LonghornEngineer/DOOM_SAO/Software/DOOM_SAO/DG_Faces.h

/*****************************************************************************
 * Made with beer and late nights in California and Texas.
 *
 * (C) Copyright 2017-2019 AND!XOR LLC (https://andnxor.com/).
 *
 * PROPRIETARY AND CONFIDENTIAL UNTIL AUGUST 11th, 2019 then,
 *
 * Licensed under the Apache License, Version 2.0 (the "License");
 * you may not use this file except in compliance with the License.
 * You may obtain a copy of the License at
 *
 *     http://www.apache.org/licenses/LICENSE-2.0
 *
 * Unless required by applicable law or agreed to in writing, software
 * distributed under the License is distributed on an "AS IS" BASIS,
 * WITHOUT WARRANTIES OR CONDITIONS OF ANY KIND, either express or implied.
 * See the License for the specific language governing permissions and
 * limitations under the License.
 *
 * ADDITIONALLY:
 * If you find this source code useful in anyway, use it in another electronic
 * conference badge, or just think it's neat. Consider buying us a beer
 * (or two) and/or a badge (or two). We are just as obsessed with collecting
 * badges as we are in making them.
 *
 * Contributors:
 *  @Cr4bf04m
 *  @andnxor
 *  @zappbrandnxor
 *  @hyr0n1
 *  @bender_andnxor
 *  @lacosteaef
 *  @f4nci3
 ****************************************************************************
 */
 
/*
 * Contains all the Doomguy Faces
 * 
 * dg_FullHP_left
 * dg_FullHP_middle
 * dg_FullHP_right
 * dg_FullHP_angry_left
 * dg_FullHP_angry_middle
 * dg_FullHP_angry_right
 * dg_FullHP_damage
 * dg_FullHP_evil
 * dg_80HP_left
 * dg_80HP_middle
 * dg_80HP_right
 * dg_80HP_angry_left
 * dg_80HP_angry_middle
 * dg_80HP_angry_right
 * dg_60HP_left
 * dg_60HP_middle
 * dg_60HP_right
 * dg_60HP_angry_left
 * dg_60HP_angry_middle
 * dg_60HP_angry_right
 * dg_40HP_left
 * dg_40HP_middle
 * dg_40HP_right
 * dg_40HP_angry_left
 * dg_40HP_angry_middle
 * dg_40HP_angry_right
 * dg_20HP_left
 * dg_20HP_middle
 * dg_20HP_right
 * dg_20HP_angry_left
 * dg_20HP_angry_middle
 * dg_20HP_angry_right
 * dg_dead
 * dg_god_mode
 * 
 */

const uint16_t dg_FullHP_left[780] = {
  0xffff, 0xffff, 0xffff, 0xffff, 0xffff, 0xffff, 0x51a2, 0x6a03, 0x6a03, 0x6a03, 0x7224, 0x8264, 0x8264, 0x8264, 0x8264, 0x8264, 
  0x7224, 0x6a03, 0x6a03, 0x51a2, 0xffff, 0xffff, 0xffff, 0xffff, 0xffff, 0xffff, 0xffff, 0xffff, 0xffff, 0xffff, 0x3121, 0x6a03, 
  0x51a2, 0x6a03, 0x6a03, 0x6a03, 0x7224, 0x8264, 0x8264, 0x8264, 0x8264, 0x8264, 0x7224, 0x6a03, 0x6a03, 0x51a2, 0x6a03, 0x3121, 
  0xffff, 0xffff, 0xffff, 0xffff, 0xffff, 0xffff, 0xffff, 0x3121, 0x3121, 0x6a03, 0x59e2, 0x8a85, 0x9ae6, 0xbb67, 0xd3e8, 0xe429, 
  0xe429, 0xe429, 0xd3e8, 0xbb67, 0xab06, 0x8264, 0x6a03, 0x59e2, 0x6a03, 0x3121, 0x3121, 0xffff, 0xffff, 0xffff, 0xffff, 0xffff, 
  0xffff, 0x3121, 0x6a03, 0x8264, 0x9ae6, 0xbb67, 0xd3e8, 0xe409, 0xe429, 0xd3e8, 0xc3a8, 0xab06, 0xab06, 0xab06, 0x9ae6, 0x9ae6, 
  0x8264, 0x8264, 0x59e2, 0x51a2, 0x3121, 0xffff, 0xffff, 0xffff, 0xffff, 0xffff, 0x28e0, 0x3121, 0x8264, 0x92a5, 0x8264, 0x9ae6, 
  0xab06, 0xc3a8, 0x92a5, 0xbb67, 0x9ae6, 0xb347, 0x8264, 0x8264, 0x8264, 0x8264, 0x6a03, 0x59e2, 0x3121, 0x3121, 0x28e0, 0x28e0, 
  0xffff, 0xffff, 0xffff, 0xffff, 0x28e0, 0x4141, 0x6a03, 0x8264, 0x6a03, 0x9ae6, 0xab06, 0x9ae6, 0x9ae6, 0x9ae6, 0x9ae6, 0x51a2, 
  0x9ae6, 0x6a03, 0x51a2, 0x6a03, 0x51a2, 0x3121, 0x28e0, 0x28e0, 0x28e0, 0x28e0, 0xffff, 0xffff, 0xffff, 0xffff, 0x28e0, 0x4141, 
  0x51a2, 0x59e2, 0x6a03, 0x9ae6, 0x59e2, 0xab06, 0x7224, 0x7224, 0x9ae6, 0x7224, 0x51a2, 0x7224, 0x51a2, 0x4141, 0x6a03, 0x28e0, 
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
  0x7101, 0xa2e6, 0xf48b, 0xf48b, 0x9ac5, 0x7101, 0xb9a7, 0xec4a, 0xf4cc, 0xdbe8, 0x8a85, 0xab46, 0xcdb4, 0xffff, 0xffff, 0xffff, 
  0xffff, 0xffff, 0xffff, 0xffff, 0xe656, 0x8a84, 0xcbc8, 0xe429, 0xdb2a, 0xbac7, 0x7841, 0x70e1, 0x92c6, 0x92c6, 0x78e2, 0x7000, 
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
};
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
