LonghornEngineer/DOOM_SAO/Software/DOOM_SAO/MF_Logo.h

/*****************************************************************************
 * Made with beer and late nights in California and Texas.
 *
 * (C) Copyright 2017-2019 AND!XOR LLC (https://andnxor.com/).
 *
 * PROPRIETARY AND CONFIDENTIAL UNTIL AUGUST 11th, 2019 then,
 *
 * Licensed under the Apache License, Version 2.0 (the "License");
 * you may not use this file except in compliance with the License.
 * You may obtain a copy of the License at
 *
 *     http://www.apache.org/licenses/LICENSE-2.0
 *
 * Unless required by applicable law or agreed to in writing, software
 * distributed under the License is distributed on an "AS IS" BASIS,
 * WITHOUT WARRANTIES OR CONDITIONS OF ANY KIND, either express or implied.
 * See the License for the specific language governing permissions and
 * limitations under the License.
 *
 * ADDITIONALLY:
 * If you find this source code useful in anyway, use it in another electronic
 * conference badge, or just think it's neat. Consider buying us a beer
 * (or two) and/or a badge (or two). We are just as obsessed with collecting
 * badges as we are in making them.
 *
 * Contributors:
 *  @Cr4bf04m
 *  @andnxor
 *  @zappbrandnxor
 *  @hyr0n1
 *  @bender_andnxor
 *  @lacosteaef
 *  @f4nci3
 ****************************************************************************
 */

/*
 * Contains MF Logo
 * 
 */

const uint16_t MF_Logo[3600] = {
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
  0xea2a, 0xea2a, 0xea2a, 0xea2a, 0xea2a, 0xea2a, 0xea2a, 0xea09, 0xea4a, 0xfe39, 0xffff, 0xffff, 0xffff, 0xffff, 0xffff, 0xffff, 
  0xffff, 0xffff, 0xffff, 0xffff, 0xffff, 0xffff, 0xffff, 0xffff, 0xffff, 0xffff, 0xffff, 0xffff, 0xffff, 0xffff, 0xffff, 0xffff, 
  0xffff, 0xffff, 0xffff, 0xffff, 0xffff, 0xffff, 0xffff, 0xffff, 0xffff, 0xffff, 0xffff, 0xffff, 0xffff, 0xfe39, 0xea4a, 0xea2a, 
  0xea2a, 0xea2a, 0xea2a, 0xea2a, 0xea2a, 0xea2a, 0xea2a, 0xea09, 0xf34e, 0xffbe, 0xff1c, 0xf2ec, 0xea2a, 0xea2a, 0xea2a, 0xea2a, 
  0xea2a, 0xea2a, 0xea2a, 0xea2a, 0xea2a, 0xea2a, 0xfe39, 0xffff, 0xffff, 0xffff, 0xffff, 0xffff, 0xffff, 0xffff, 0xffff, 0xffff, 
  0xffff, 0xffff, 0xffff, 0xffff, 0xffff, 0xffff, 0xffff, 0xffff, 0xffff, 0xffff, 0xffff, 0xffff, 0xffff, 0xffff, 0xffff, 0xffff, 
  0xffff, 0xffff, 0xffff, 0xffff, 0xffff, 0xffff, 0xffff, 0xffff, 0xfe18, 0xea4a, 0xea2a, 0xea2a, 0xea2a, 0xea2a, 0xea2a, 0xea2a, 
  0xea2a, 0xea2a, 0xea09, 0xf2ed, 0xff7d, 0xffff, 0xffff, 0xff3d, 0xf2ed, 0xea09, 0xea2a, 0xea2a, 0xea2a, 0xea2a, 0xea2a, 0xea2a, 
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
};
